VilleHiltunen/helvar-testing-rig/frame_cad/sensor_mounting_plate.stp

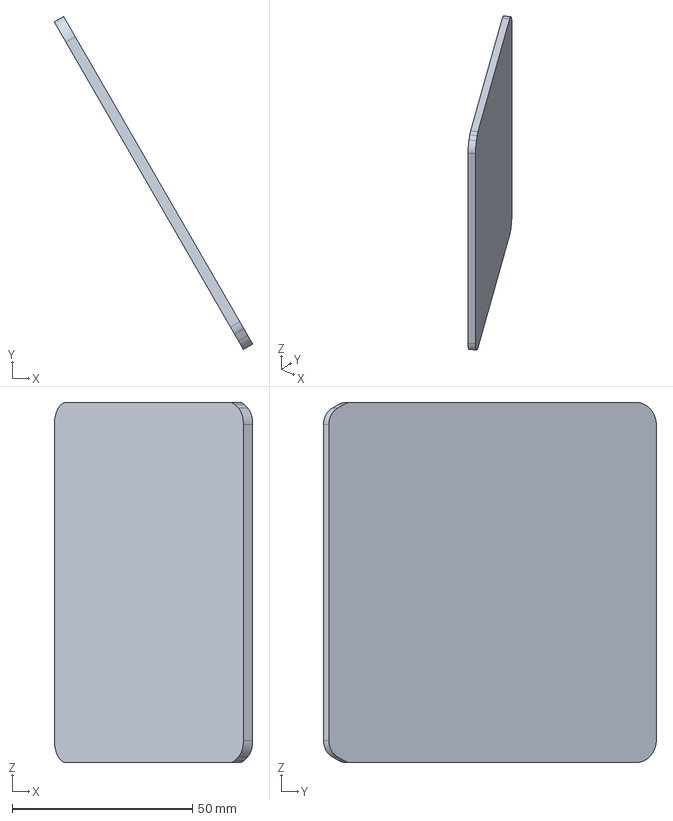
[picture p15: CAD file, 2019-09-02]
frame_cad/sensor_mounting_plate.stp
55.1 x 92.4 x 100.0 mm
