VilleHiltunen/helvar-testing-rig/Testing_unit/Body/Body_151mm/side_151mm.step

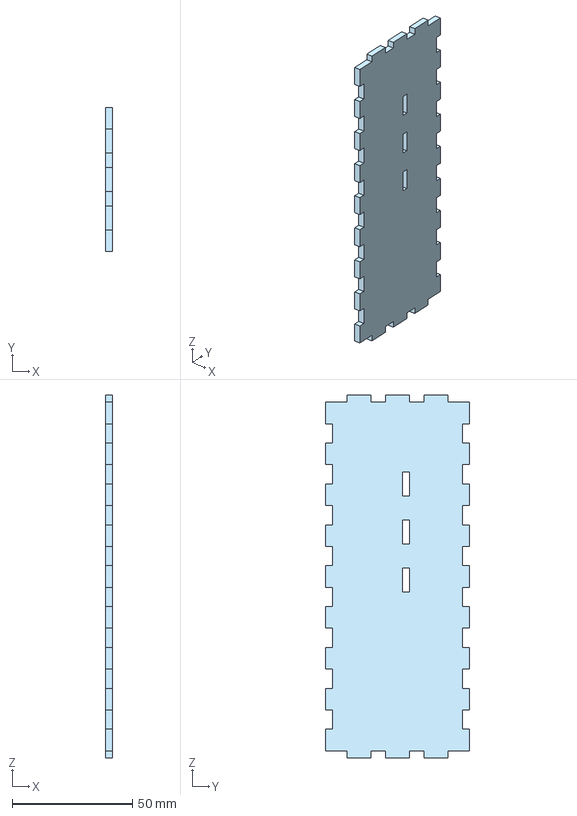
[picture p16: CAD file, 2019-09-02]
Testing_unit/Body/Body_151mm/side_151mm.step
3.00 x 60.0 x 151.0 mm
