VilleHiltunen/helvar-testing-rig/Testing_unit/Body/Body_168mm/side_168mm.step

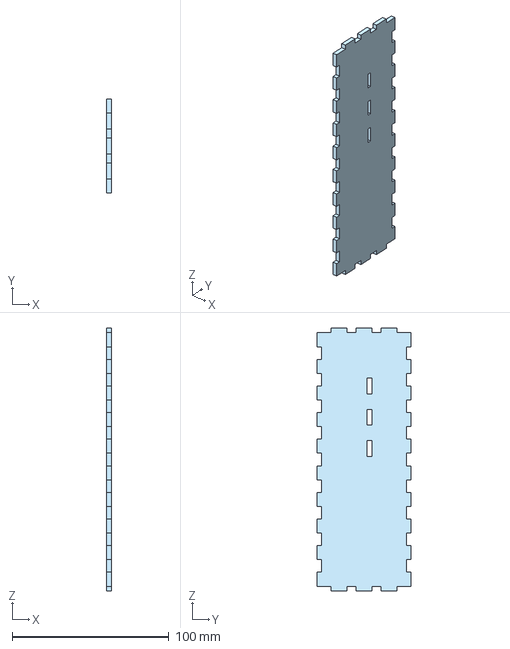
[picture p17: CAD file, 2019-09-02]
Testing_unit/Body/Body_168mm/side_168mm.step
3.00 x 60.0 x 168.0 mm
