VilleHiltunen/helvar-testing-rig/Testing_unit/Body/Common parts/bottom_plate.step

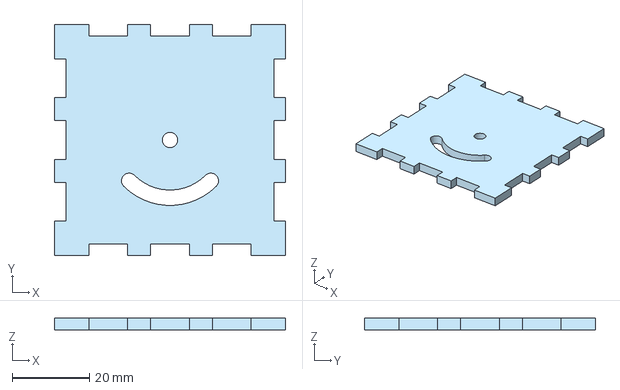
[picture p18: CAD file, 2019-09-02]
Testing_unit/Body/Common parts/bottom_plate.step
60.0 x 60.0 x 3.00 mm
