VilleHiltunen/helvar-testing-rig/Testing_unit/Head/head_holder.step

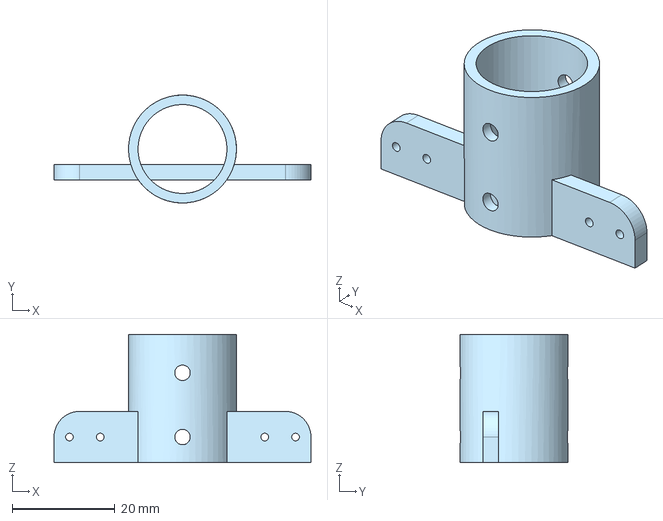
[picture p19: CAD file, 2019-09-02]
Testing_unit/Head/head_holder.step
50.0 x 21.0 x 25.0 mm
