VilleHiltunen/helvar-testing-rig/Testing_unit/Body/Body_117mm/side_117mm.step

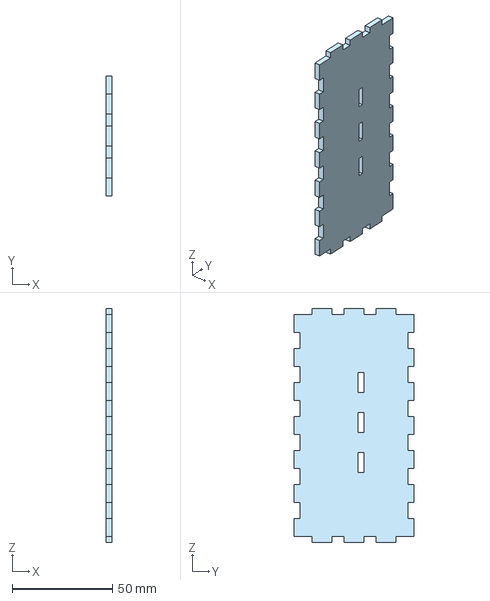
[picture p20: CAD file, 2019-09-02]
Testing_unit/Body/Body_117mm/side_117mm.step
3.00 x 60.0 x 117.0 mm
