VilleHiltunen/helvar-testing-rig/Testing_unit/Body/Body_134mm/side_134mm.step

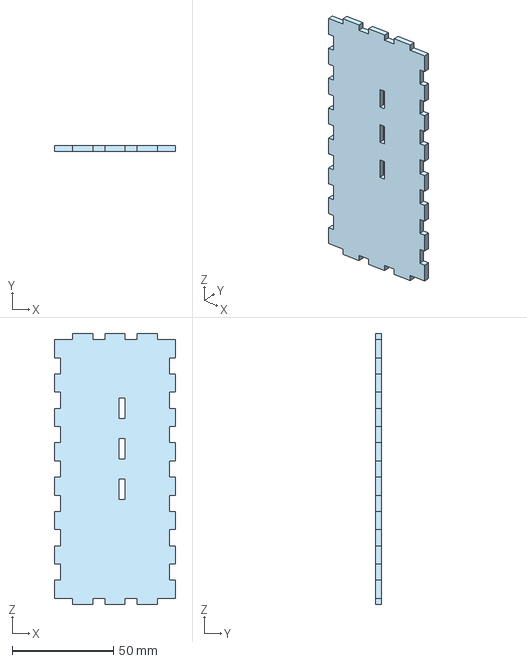
[picture p21: CAD file, 2019-09-02]
Testing_unit/Body/Body_134mm/side_134mm.step
60.0 x 3.00 x 134.0 mm
