VilleHiltunen/helvar-testing-rig/Testing_unit/Head/head.step

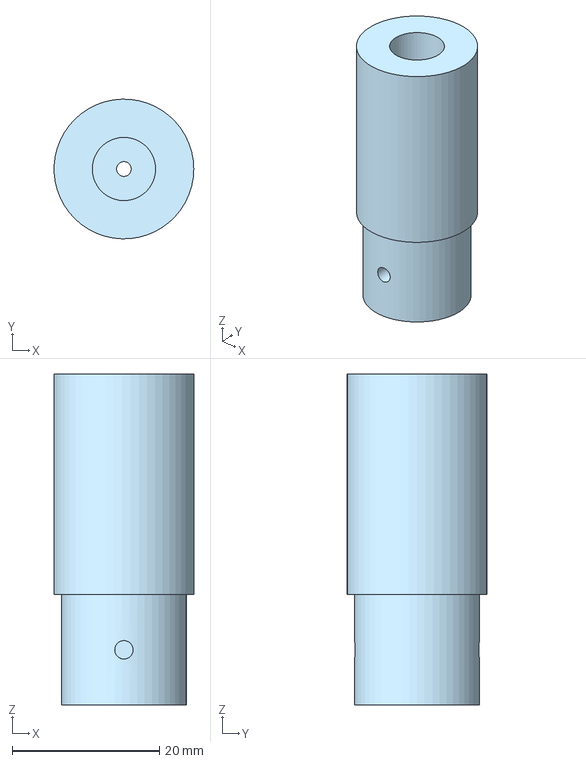
[picture p23: CAD file, 2019-09-02]
Testing_unit/Head/head.step
19.0 x 19.0 x 45.0 mm
